bluetailtech/p25rx_display/usb_host/usbh_conf.h

/**
  ******************************************************************************
  * @file    USB_Host/CDC_Standalone/Inc/usbh_conf.h
  * @author  MCD Application Team
  * @brief   General low level driver configuration
  ******************************************************************************
  * @attention
  *
  * <h2><center>&copy; Copyright (c) 2017 STMicroelectronics International N.V.
  * All rights reserved.</center></h2>
  *
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
  ******************************************************************************
  */

/* Define to prevent recursive inclusion -------------------------------------*/
#ifndef __USBH_CONF_H
#define __USBH_CONF_H

/* Includes ------------------------------------------------------------------*/
#include "stm32h7xx_hal.h"
#include <stdio.h>
#include <stdlib.h>
#include <string.h>
#include "std_io.h"

/* Exported types ------------------------------------------------------------*/
#define USBH_MAX_NUM_ENDPOINTS                2
#define USBH_MAX_NUM_INTERFACES               2
#define USBH_MAX_NUM_CONFIGURATION            1
#define USBH_MAX_NUM_SUPPORTED_CLASS          1
#define USBH_KEEP_CFG_DESCRIPTOR              0
#define USBH_MAX_SIZE_CONFIGURATION           0x200
#define USBH_MAX_DATA_BUFFER                  0x200
#define USBH_DEBUG_LEVEL                      3
#define USBH_USE_OS                           0
#define USE_HAL_HCD_REGISTER_CALLBACKS 1

/* Exported constants --------------------------------------------------------*/
/* Exported macro ------------------------------------------------------------*/
/* CMSIS OS macros */
#if (USBH_USE_OS == 1)
#include "cmsis_os.h"
#define   USBH_PROCESS_PRIO    osPriorityNormal
#endif

/* Memory management macros */
#define USBH_malloc               malloc
#define USBH_free                 free
#define USBH_memset               memset
#define USBH_memcpy               memcpy


#define USBH_UsrLog printf
#define USBH_ErrLog printf
#define USBH_DbgLog

/* Exported functions ------------------------------------------------------- */

#endif /* __USBH_CONF_H */

/************************ (C) COPYRIGHT STMicroelectronics *****END OF FILE****/
