bluetailtech/p25rx_display/lcd_ili9341/xy_plot.h

#ifndef _ILI9341H_XYPLOTDATA
#define _ILI9341H_XYPLOTDATA

//MIT License
//
//Copyright (c) 2020 tvelliott
//
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
int xy_plot[] = {
  202, 67,
  202, 67,
  202, 67,
  202, 67,
  202, 67,
  202, 69,
  193, 69,
  191, 74,
  192, 74,
  193, 74,
  202, 74,
  202, 74,
  203, 74,
  208, 74,
  203, 69,
  202, 69,
  202, 69,
  202, 69,
  202, 69,
  194, 69,
  193, 74,
  193, 74,
  196, 65,
  202, 62,
  208, 69,
  208, 69,
  208, 67,
  208, 67,
  202, 67,
  202, 66,
  194, 67,
  194, 67,
  196, 69,
  202, 69,
  202, 69,
  208, 69,
  208, 74,
  202, 67,
  202, 67,
  196, 67,
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
};
int xy_plot_len = 126;

#endif
